walklinewang/Radial-Controller/src/Drivers/EEPROM.h

/*
  EEPROM 配置参数存储驱动头文件

  Copyright © 2026 Walkline Wang (walkline@gmail.com)
  Github: https://github.com/walklinewang/Radial-Controller
*/
#ifndef __EEPROM_H__
#define __EEPROM_H__

#include "../Common.h"
#include "EC11.h"
#include "MyWS2812.h"

// 配置参数存储在EEPROM中的起始地址
#define EEPROM_CONFIG_START_ADDRESS 0

// 配置结构体大小（字节）
#define CONFIG_STRUCT_SIZE sizeof(eeprom_config_t)

/**
 * @brief EEPROM 操作状态枚举
 */
typedef enum {
    EEPROM_STATUS_OK,           // 操作成功
    EEPROM_STATUS_ERROR,        // 操作错误
    EEPROM_STATUS_INVALID_PARAM // 无效参数
} eeprom_status_t;

/**
 * @brief 设备配置参数结构体
 */
typedef struct {
    uint8_t version;  // 版本号 (0)
    uint8_t revision; // 修订号 (1)

    uint8_t led_count;                // LED 灯珠数量 (2)
    ws2812_color_order_t color_order; // LED 颜色顺序 (3)
    uint8_t brightness;               // 亮度等级（0-4） (4)

    uint8_t effect_mode;      // LED 灯效模式 (5)
    uint16_t rotate_interval; // LED 流动灯效触发间隔 (6-7)
    uint16_t fade_duration;   // LED 渐变灯效持续时长 (8-9)

    int16_t rotate_cw;      // 顺时针旋转角度 (10-11)
    int16_t rotate_ccw;     // 逆时针旋转角度 (12-13)
    uint8_t step_per_teeth; // 转动一齿触发次数 (14)
    ec11_phase_t phase;     // EC11 编码器相位配置 (15)

    uint8_t reserved[16]; // 预留空间，用于未来扩展 (16-31)
} eeprom_config_t;        /* 共 32 字节 */

/**
 * @brief 获取完整的配置结构体数据指针
 * @return 配置结构体指针
 */
extern inline eeprom_config_t *EEPROM_GetConfigData();

/**
 * @brief 从 EEPROM 读取配置参数
 * @return 操作状态
 */
eeprom_status_t EEPROM_LoadConfig();

/**
 * @brief 将配置参数写入 EEPROM
 * @return 操作状态
 */
eeprom_status_t EEPROM_SaveConfig();

/**
 * @brief 重置配置参数为默认值
 * @return 操作状态
 */
eeprom_status_t EEPROM_Reset();

/**
 * @brief 验证配置参数有效性
 * @return 操作状态
 */
eeprom_status_t EEPROM_Validate();

/**
 * @brief 获取版本号
 * @return 版本号
 */
uint8_t EEPROM_GetVersion();

/**
 * @brief 获取修订号
 * @return 修订号
 */
uint8_t EEPROM_GetRevision();

/**
 * @brief 获取 LED 灯珠数量
 * @return LED 灯珠数量
 */
uint8_t EEPROM_GetLedCount();

/**
 * @brief 设置 LED 灯珠数量
 * @param count LED 灯珠数量
 * @return 操作状态
 */
eeprom_status_t EEPROM_SetLedCount(uint8_t count);

/**
 * @brief 获取 LED 颜色顺序
 * @return LED 颜色顺序（0:GRB, 1:RGB）
 */
uint8_t EEPROM_GetColorOrder();

/**
 * @brief 设置 LED 颜色顺序
 * @param order LED 颜色顺序（0:GRB, 1:RGB）
 * @return 操作状态
 */
eeprom_status_t EEPROM_SetColorOrder(uint8_t order);

/**
 * @brief 获取亮度等级
 * @return 亮度等级（0-4）
 */
uint8_t EEPROM_GetBrightness();

/**
 * @brief 设置 LED 亮度等级
 * @param brightness 亮度等级（0-4）
 * @return 操作状态
 */
eeprom_status_t EEPROM_SetBrightness(uint8_t brightness);

/**
 * @brief 获取 LED 灯效模式
 * @return LED 灯效模式
 */
uint8_t EEPROM_GetEffectMode();

/**
 * @brief 设置 LED 灯效模式
 * @param mode LED 灯效模式
 * @return 操作状态
 */
eeprom_status_t EEPROM_SetEffectMode(uint8_t mode);

/**
 * @brief 获取 LED 流动灯效触发间隔
 * @return 触发间隔（毫秒）
 */
uint16_t EEPROM_GetRotateEffectInterval();

/**
 * @brief 设置 LED 流动灯效触发间隔
 * @param interval 触发间隔（毫秒）
 * @return 操作状态
 */
eeprom_status_t EEPROM_SetRotateEffectInterval(uint16_t interval);

/**
 * @brief 获取 LED 渐变灯效持续时长
 * @return 持续时长（毫秒）
 */
uint16_t EEPROM_GetFadeEffectDuration();

/**
 * @brief 设置 LED 渐变灯效持续时长
 * @param duration 持续时长（毫秒）
 * @return 操作状态
 */
eeprom_status_t EEPROM_SetFadeEffectDuration(uint16_t duration);

/**
 * @brief 获取顺时针旋转角度
 * @return 顺时针旋转角度
 */
int16_t EEPROM_GetRotateCW();

/**
 * @brief 设置 LED 顺时针旋转角度
 * @param degrees 顺时针旋转角度
 * @return 操作状态
 */
eeprom_status_t EEPROM_SetRotateCW(int16_t degrees);

/**
 * @brief 获取 LED 逆时针旋转角度
 * @return 逆时针旋转角度
 */
int16_t EEPROM_GetRotateCCW();

/**
 * @brief 设置 LED 逆时针旋转角度
 * @param degrees 逆时针旋转角度
 * @return 操作状态
 */
eeprom_status_t EEPROM_SetRotateCCW(int16_t degrees);

/**
 * @brief 获取触发动作次数
 * @return EC11 编码器每转动一齿触发动作次数
 */
uint8_t EEPROM_GetStepPerTeeth();

/**
 * @brief 设置触发动作次数
 * @param step EC11 编码器每转动一齿触发动作次数
 * @return 操作状态
 */
eeprom_status_t EEPROM_SetStepPerTeeth(uint8_t step);

/**
 * @brief 获取 EC11 编码器相位配置
 * @return EC11 编码器相位配置
 */
ec11_phase_t EEPROM_GetPhase();

/**
 * @brief 设置 EC11 编码器相位配置
 * @param phase EC11 编码器相位配置
 * @return 操作状态
 */
eeprom_status_t EEPROM_SetPhase(ec11_phase_t phase);

#endif /* __EEPROM_H__ */
